gixhswlab1ppm/ppm/device/swing_full.png

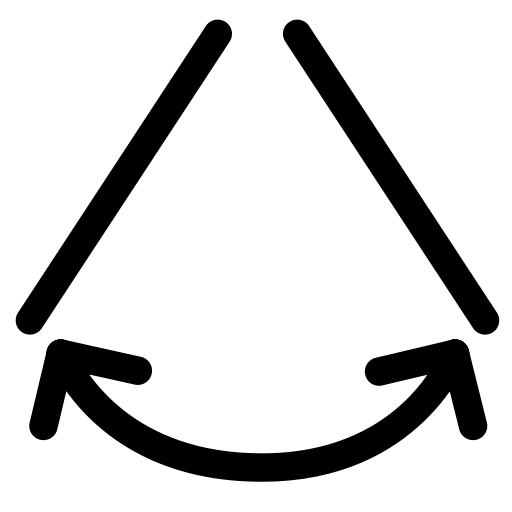
device/swing_full.png
