gixhswlab1ppm/ppm/device/thumb.png

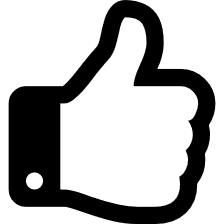
device/thumb.png
