gixhswlab1ppm/ppm/device/wave_full.png

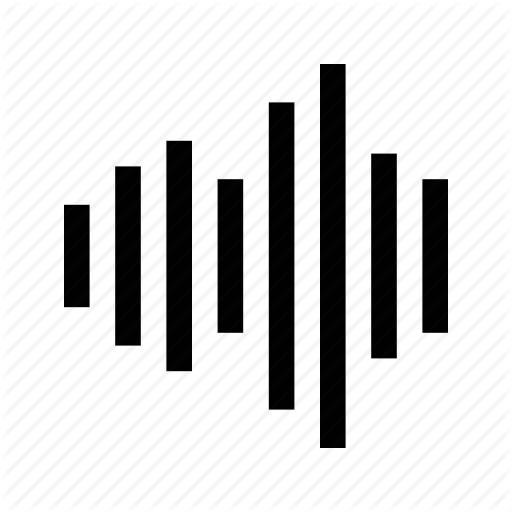
device/wave_full.png
