gixhswlab1ppm/ppm/insights/Figure_1.png

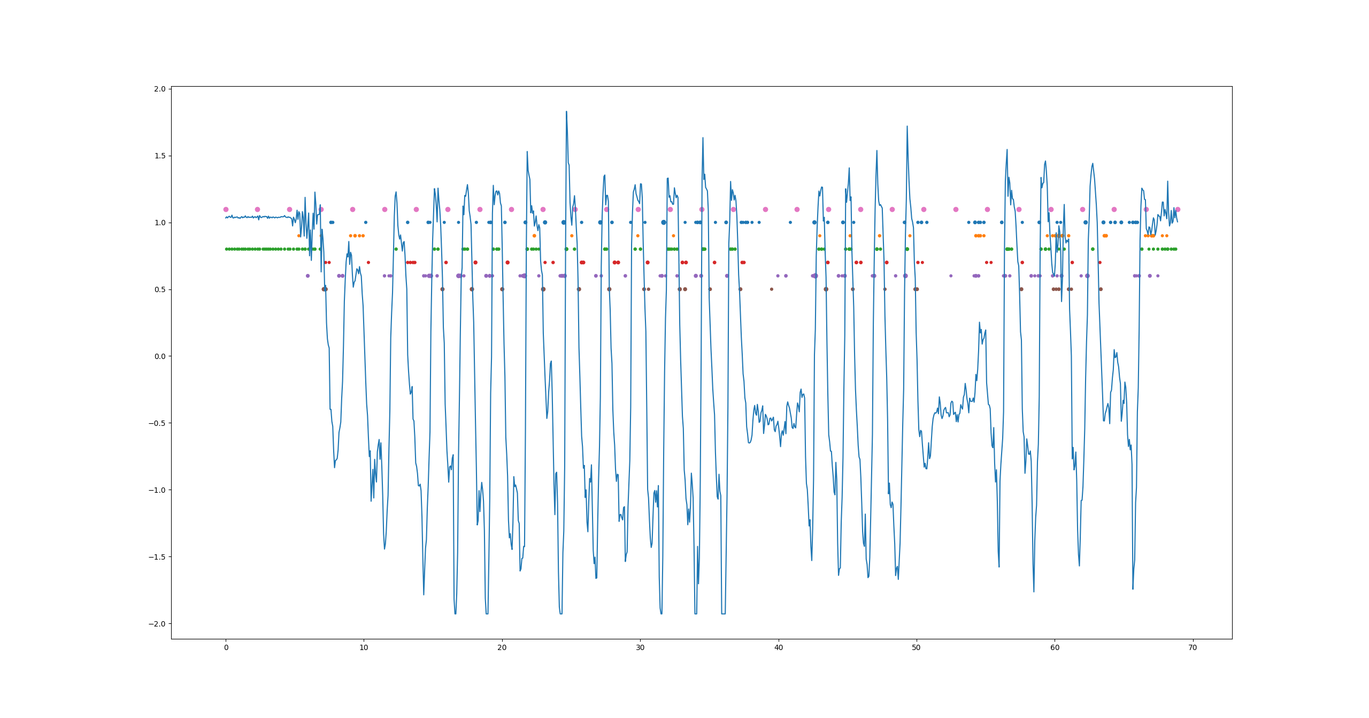
insights/Figure_1.png
