gixhswlab1ppm/ppm/insights/Figure_4.png

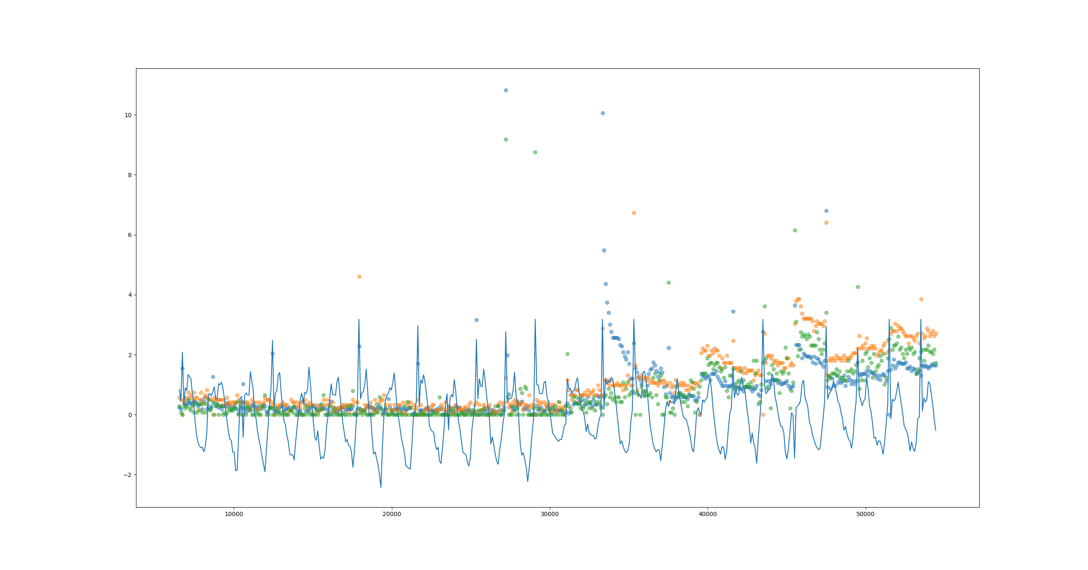
insights/Figure_4.png
