gixhswlab1ppm/ppm/insights/Figure_5.png

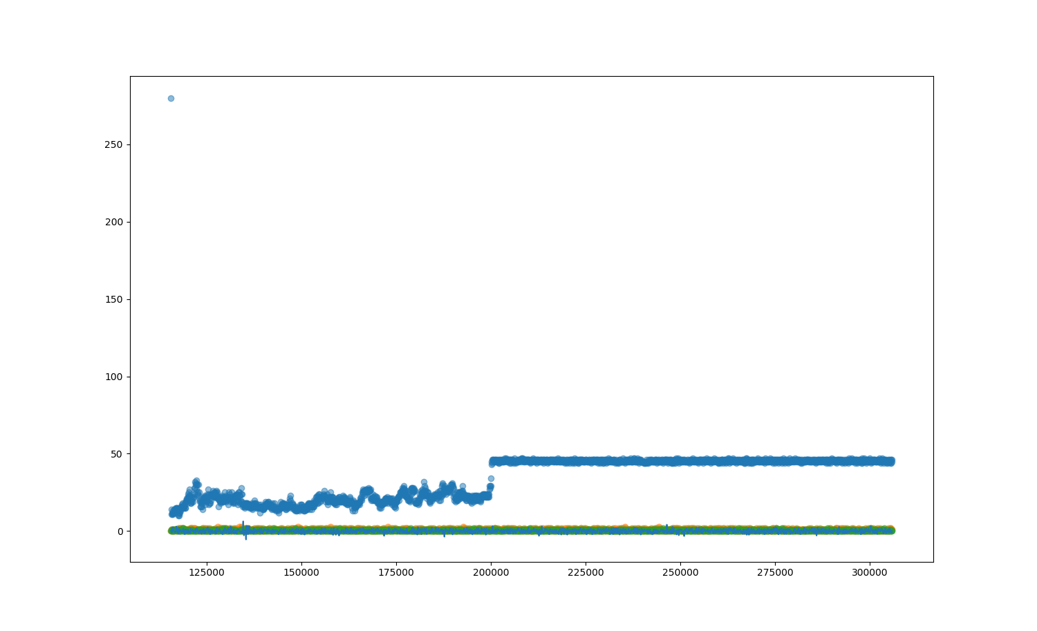
insights/Figure_5.png
