gixhswlab1ppm/ppm/insights/Figure_6.png

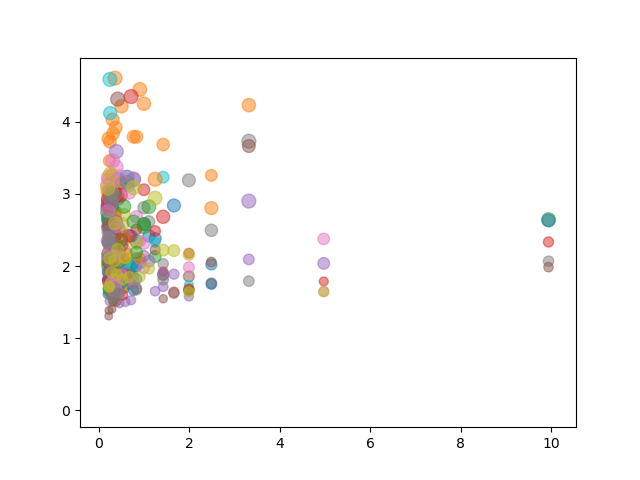
insights/Figure_6.png
