gixhswlab1ppm/ppm/insights/Figure_7.png

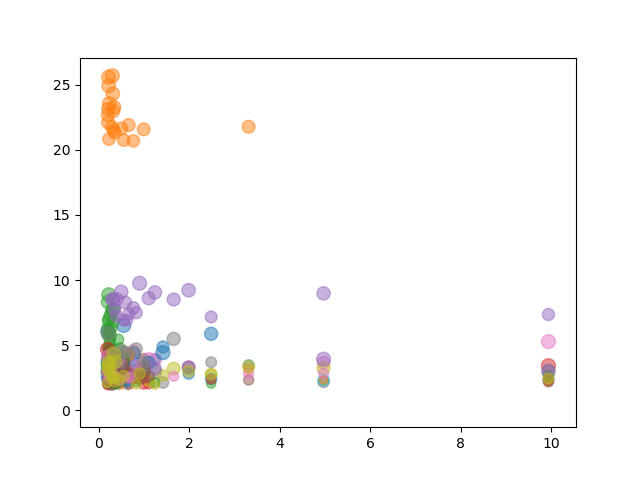
insights/Figure_7.png
