gixhswlab1ppm/ppm/insights/Figure_9.png

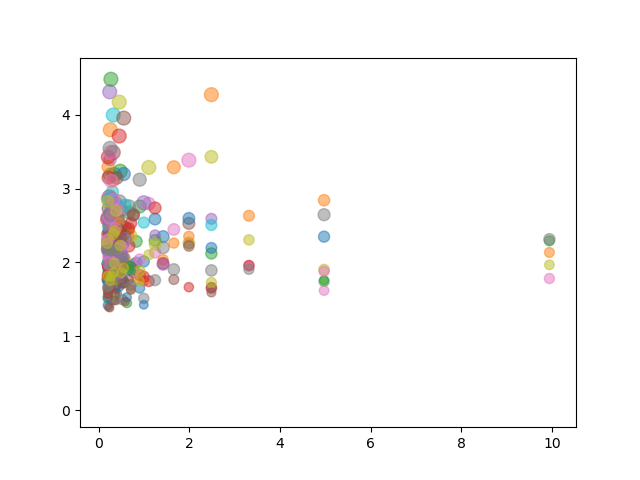
insights/Figure_9.png
