gixhswlab1ppm/ppm/insights/Figure_11.png

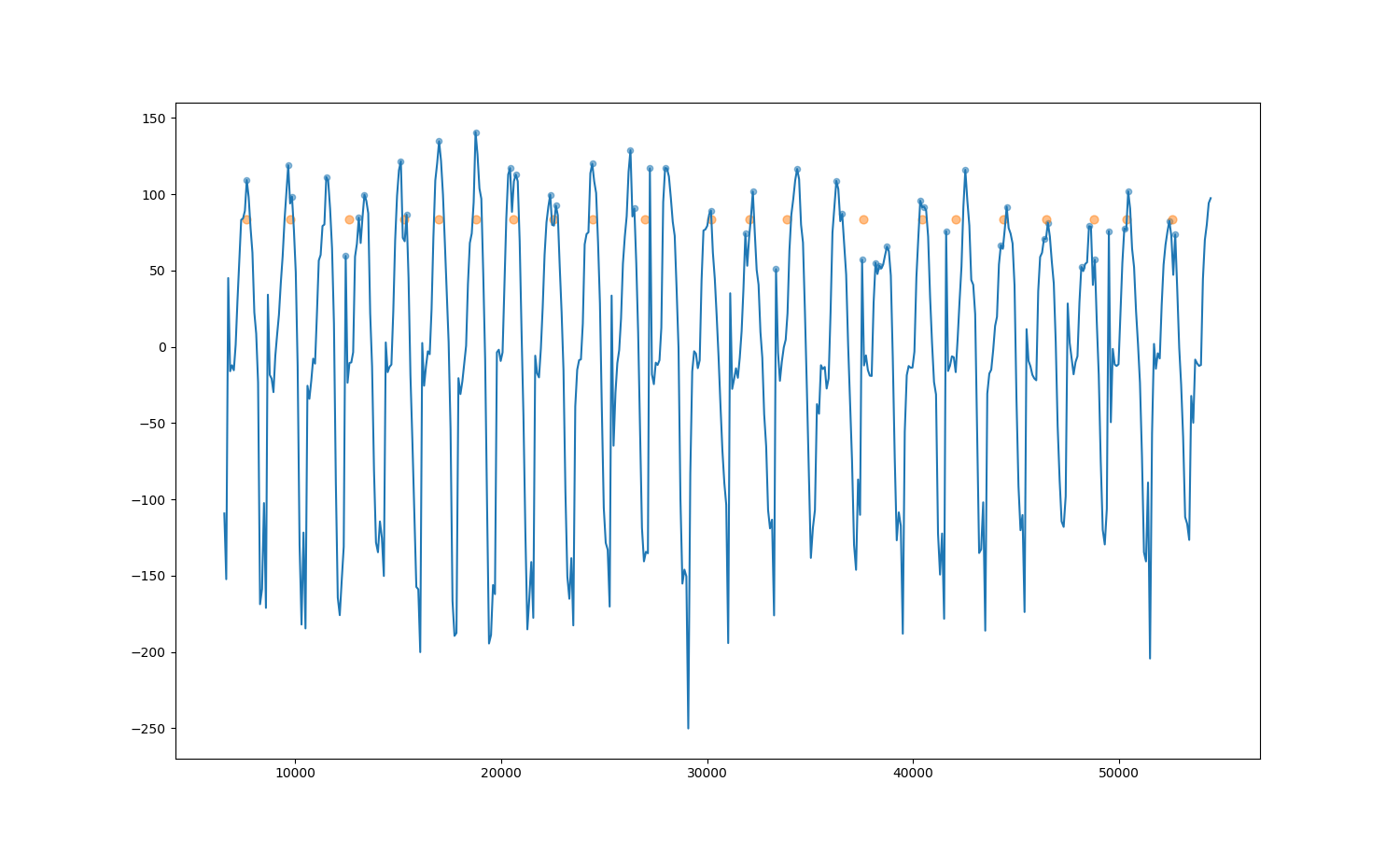
insights/Figure_11.png
