gixhswlab1ppm/ppm/insights/Figure_12.png

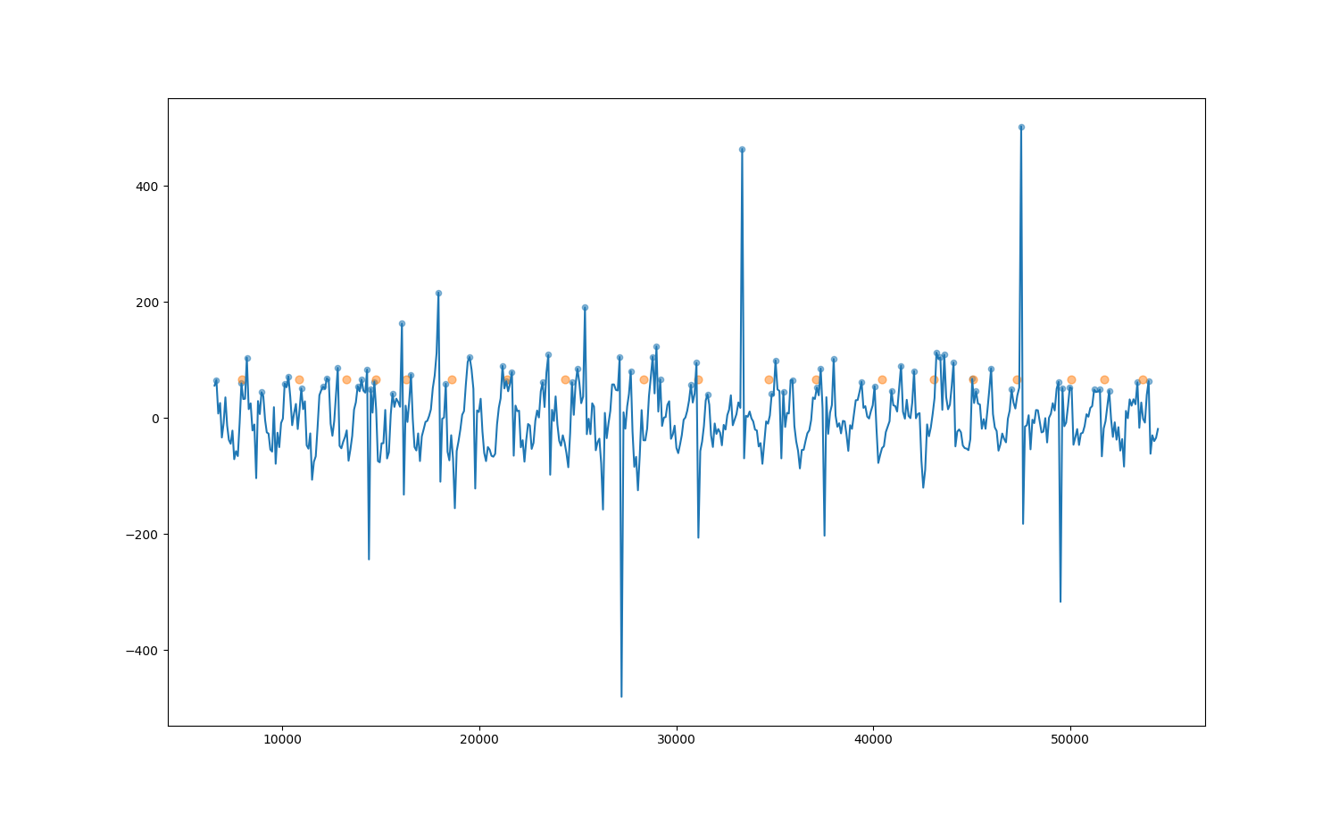
insights/Figure_12.png
