gixhswlab1ppm/ppm/insights/Figure_13.png

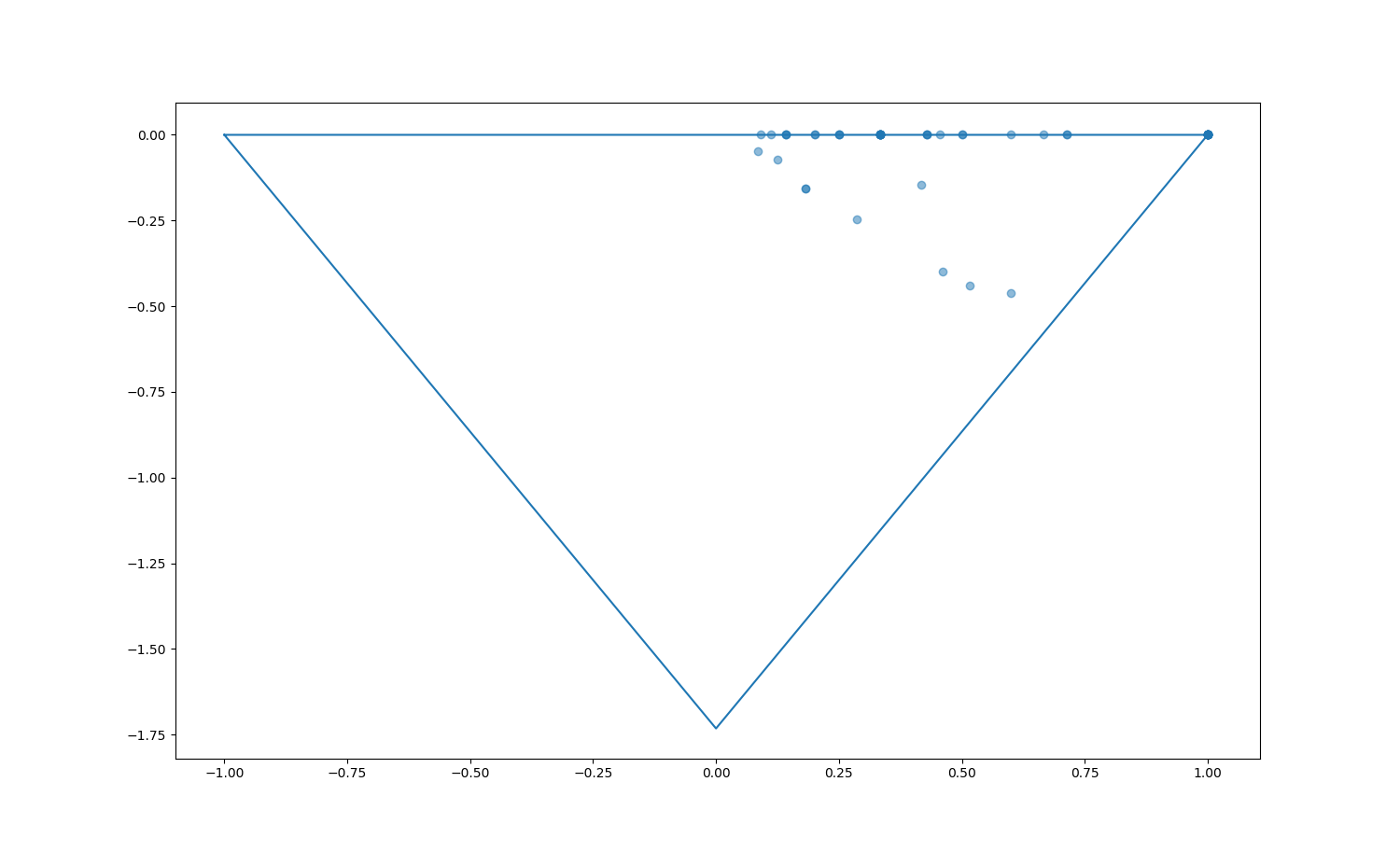
insights/Figure_13.png
