gixhswlab1ppm/ppm/insights/Figure_14.png

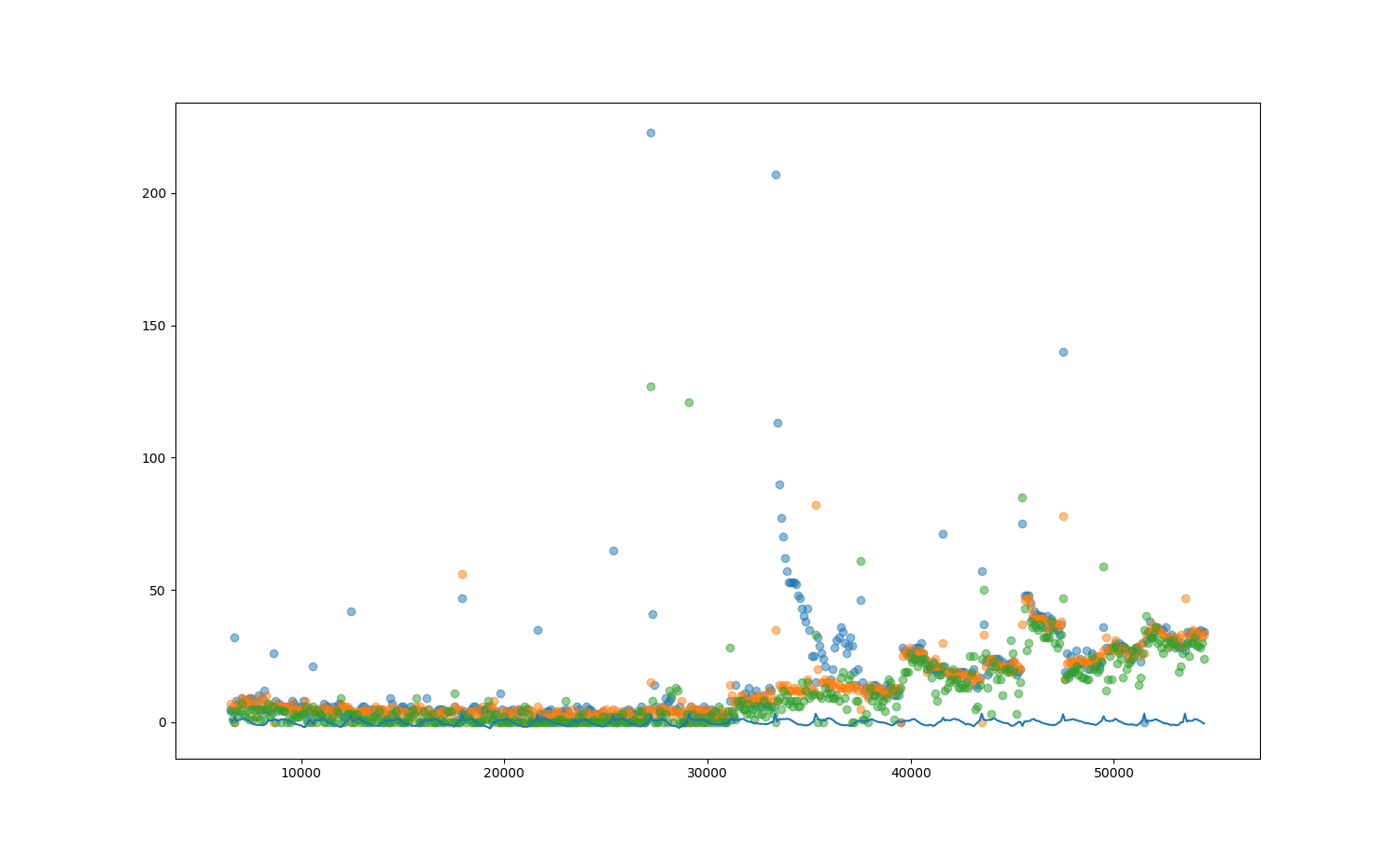
insights/Figure_14.png
