gixhswlab1ppm/ppm/insights/Figure_15.png

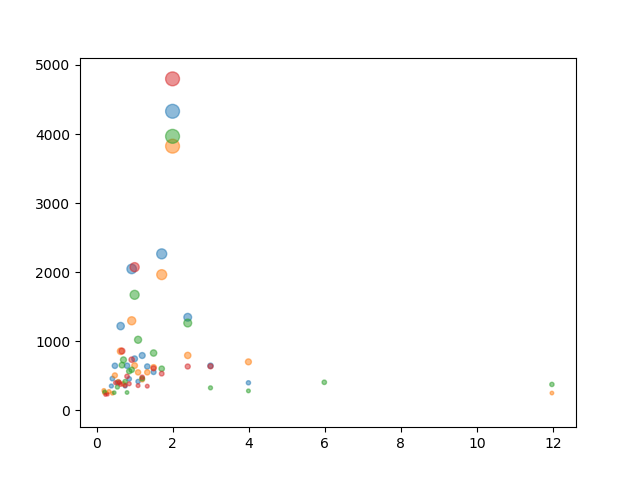
insights/Figure_15.png
