gixhswlab1ppm/ppm/insights/Figure_16.png

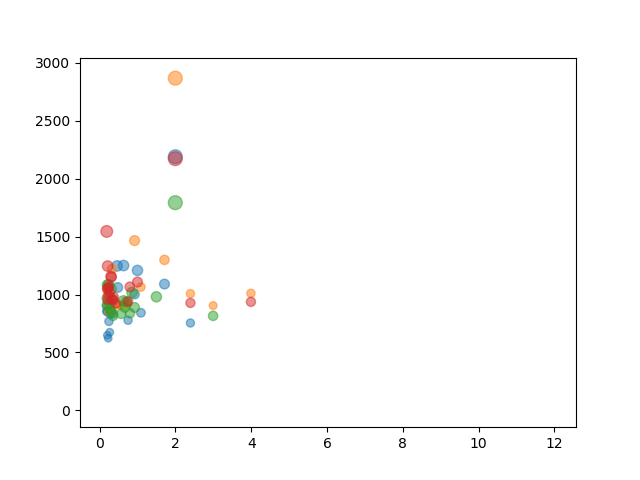
insights/Figure_16.png
