gixhswlab1ppm/ppm/insights/Figure_17.png

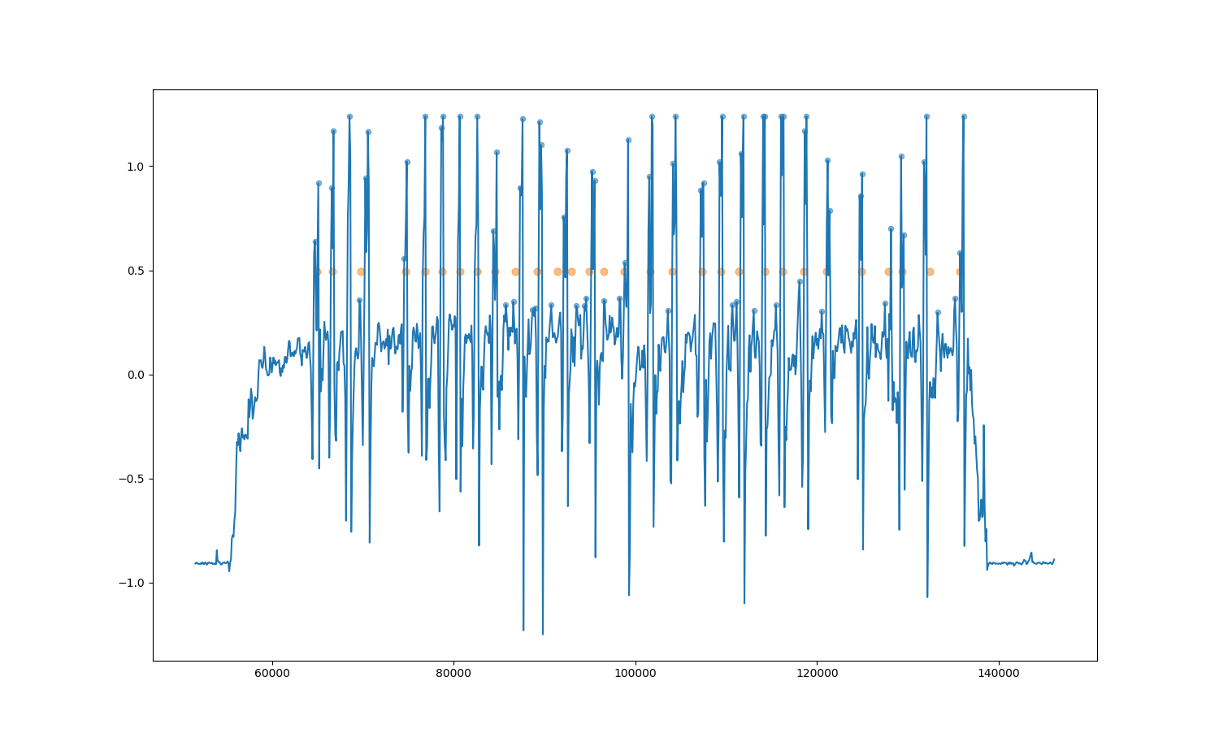
insights/Figure_17.png
