gixhswlab1ppm/ppm/insights/Figure_18.png

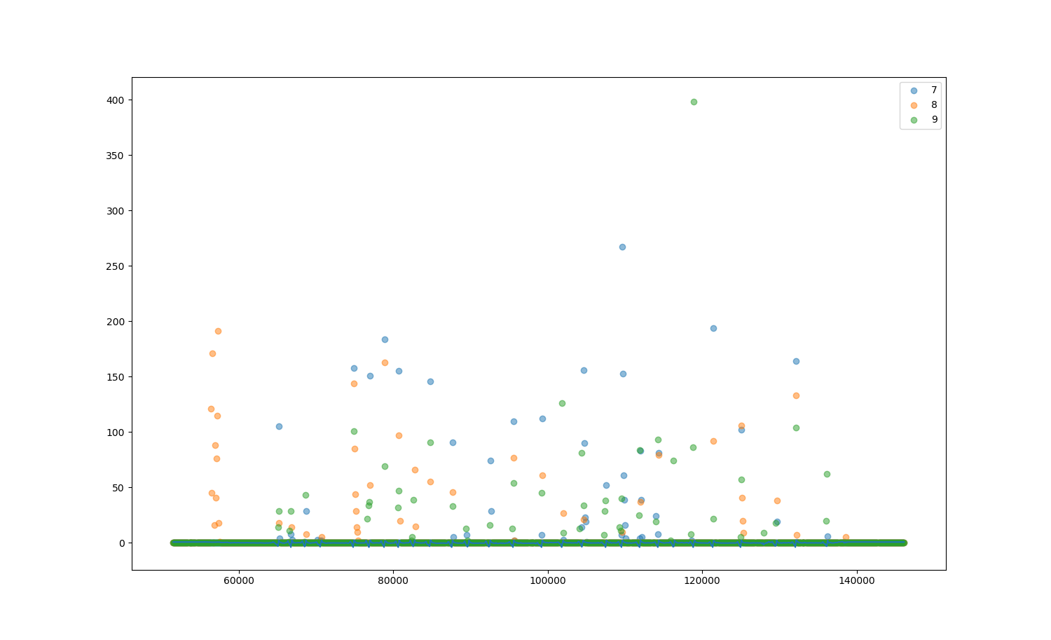
insights/Figure_18.png
