gixhswlab1ppm/ppm/insights/Figure_19.png

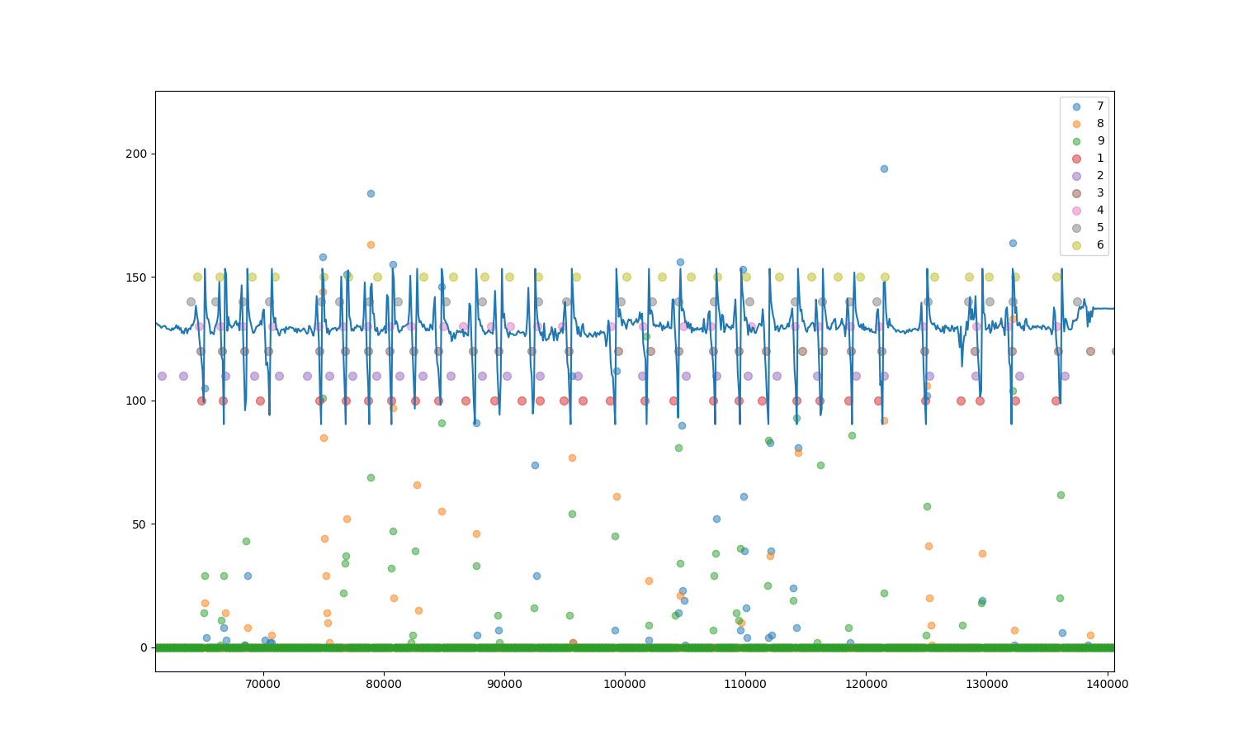
insights/Figure_19.png
