gixhswlab1ppm/ppm/insights/Figure_21.png

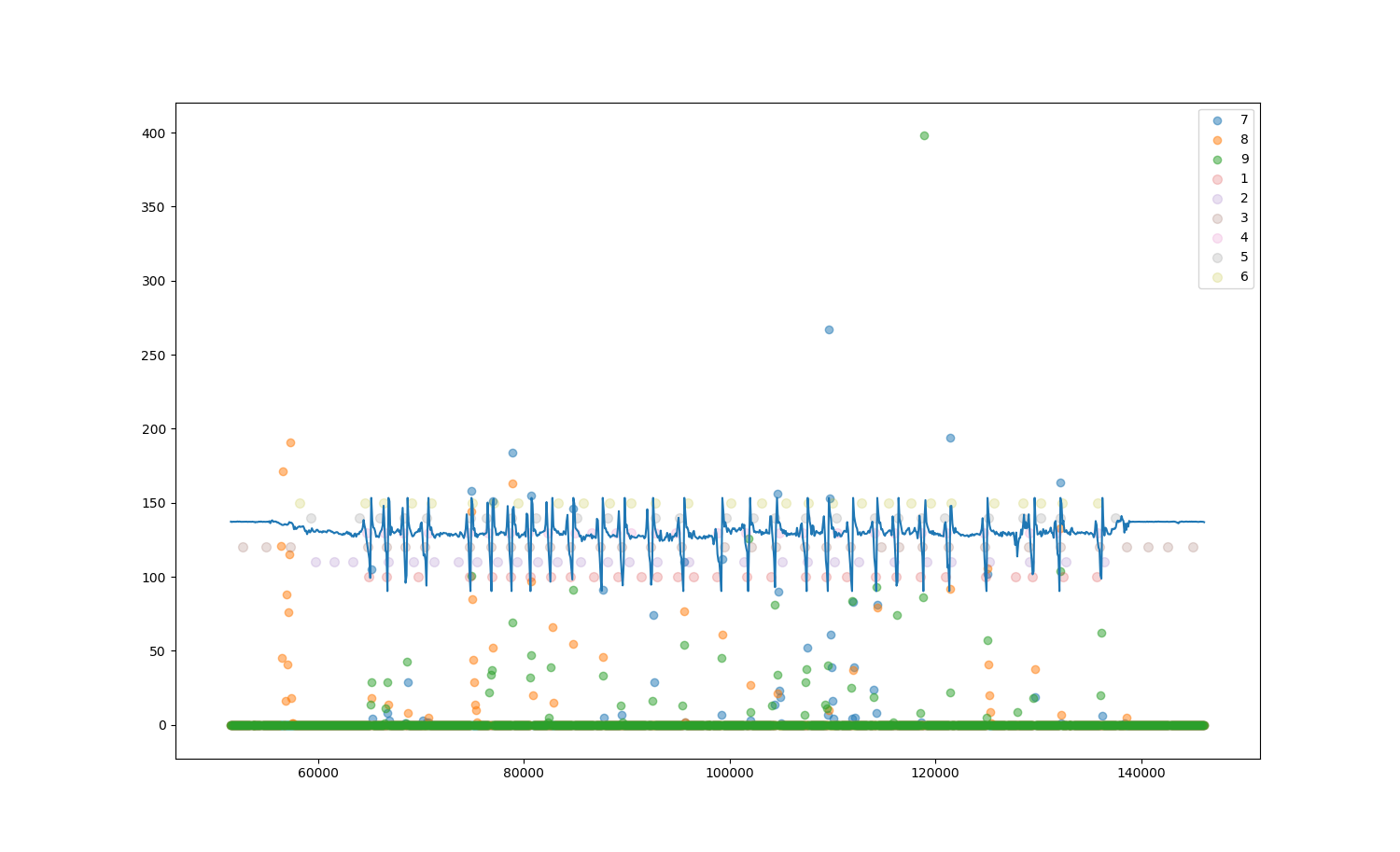
insights/Figure_21.png
