gixhswlab1ppm/ppm/insights/Figure_22.png

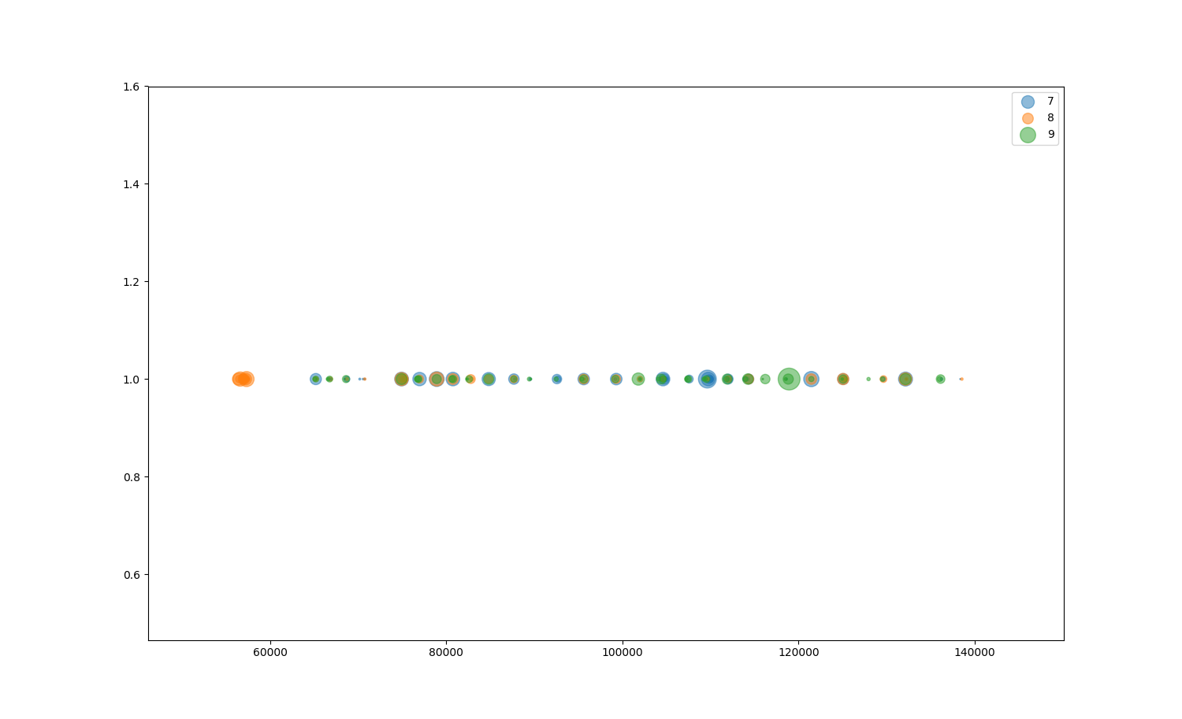
insights/Figure_22.png
