gixhswlab1ppm/ppm/insights/Figure_24.png

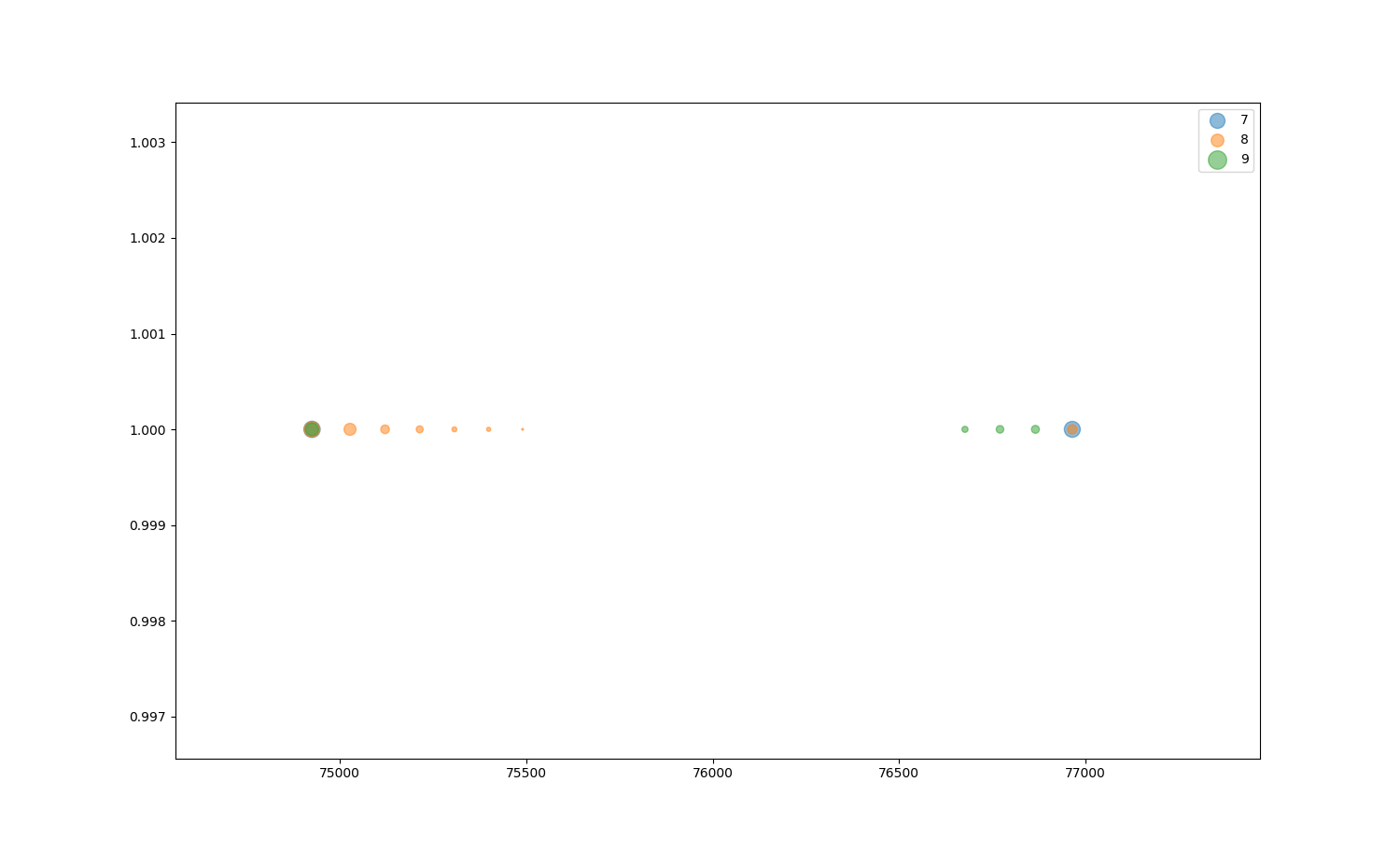
insights/Figure_24.png
