gixhswlab1ppm/ppm/insights/Figure_26.png

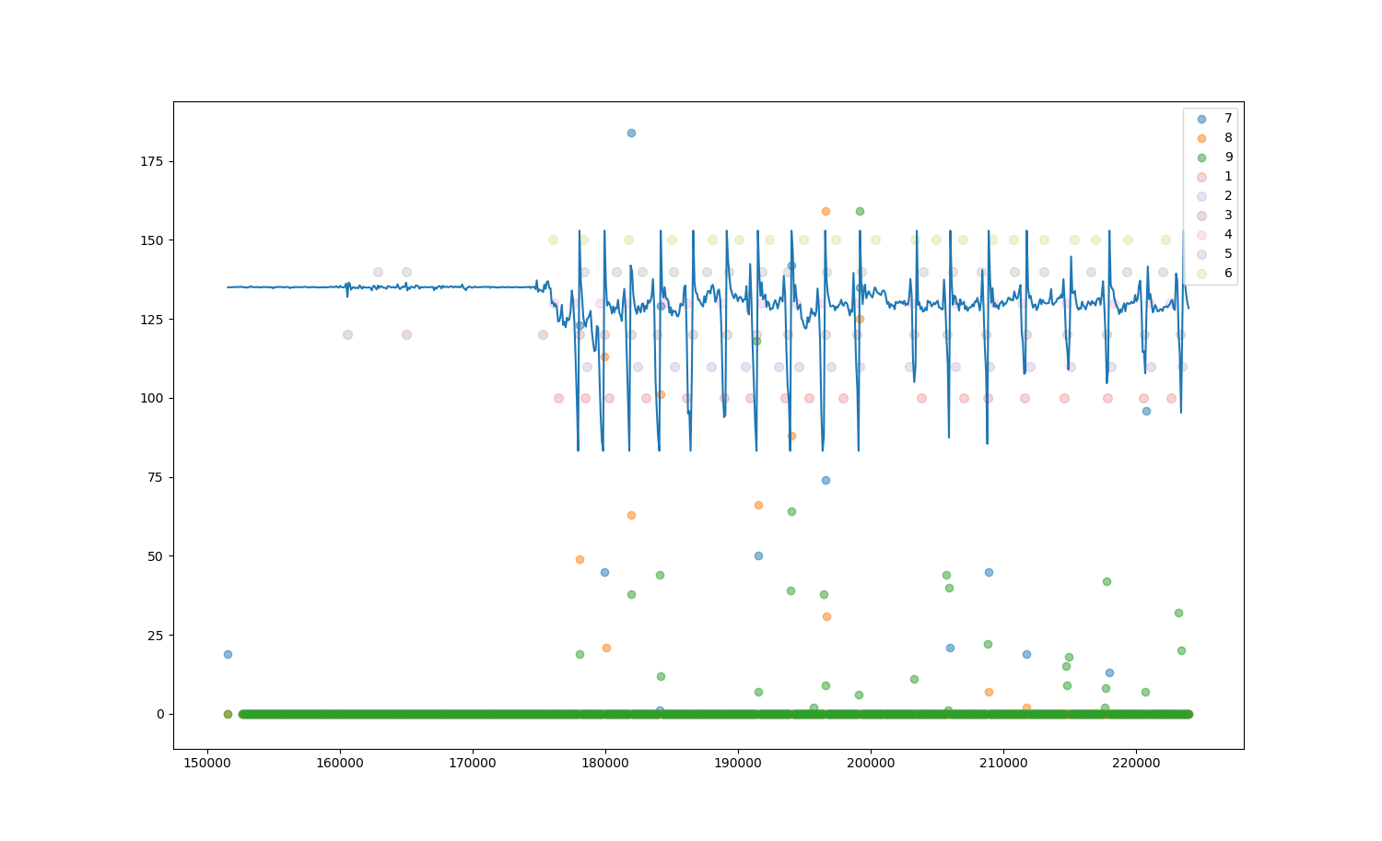
insights/Figure_26.png
