gixhswlab1ppm/ppm/insights/Figure_27.png

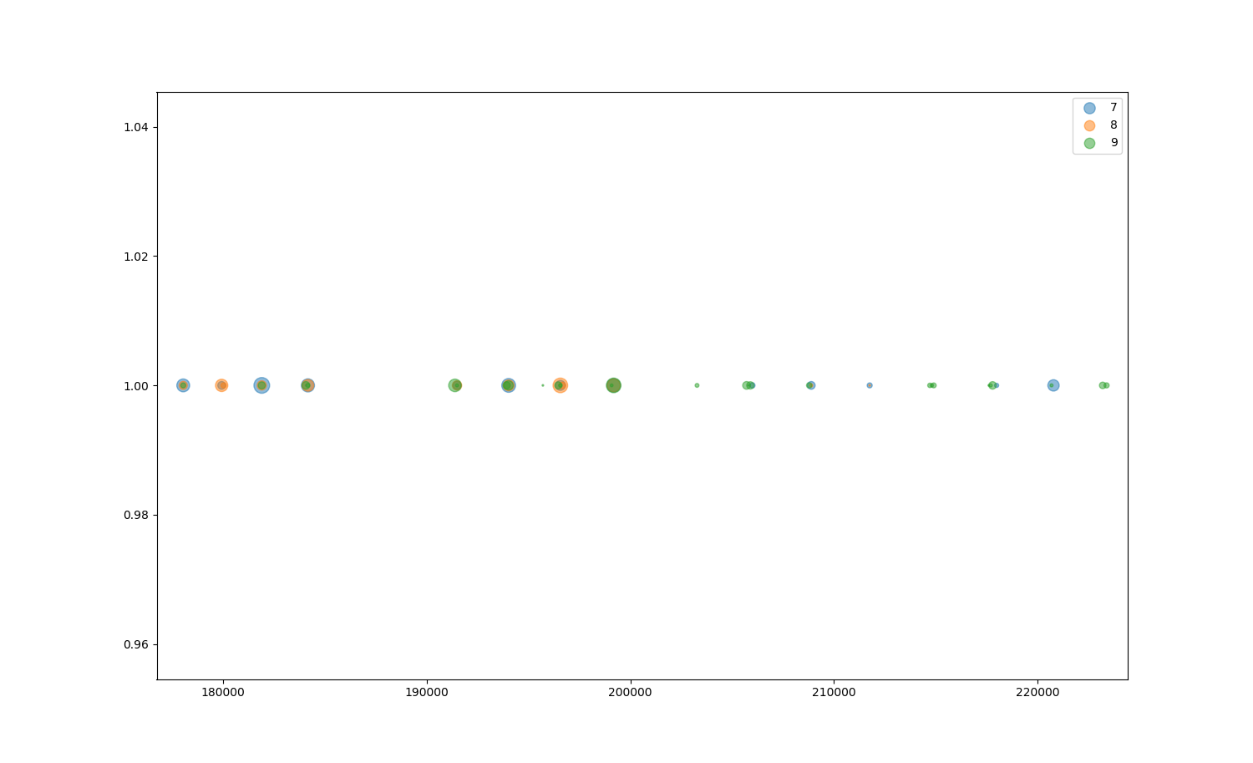
insights/Figure_27.png
