gixhswlab1ppm/ppm/insights/Figure_29.png

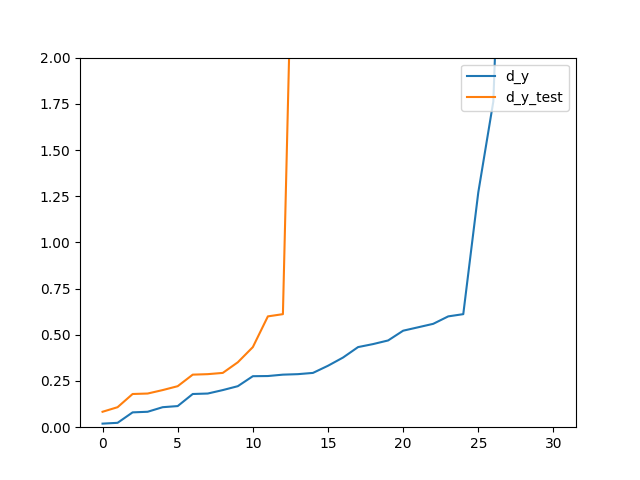
insights/Figure_29.png
