gixhswlab1ppm/ppm/insights/Figure_31.png

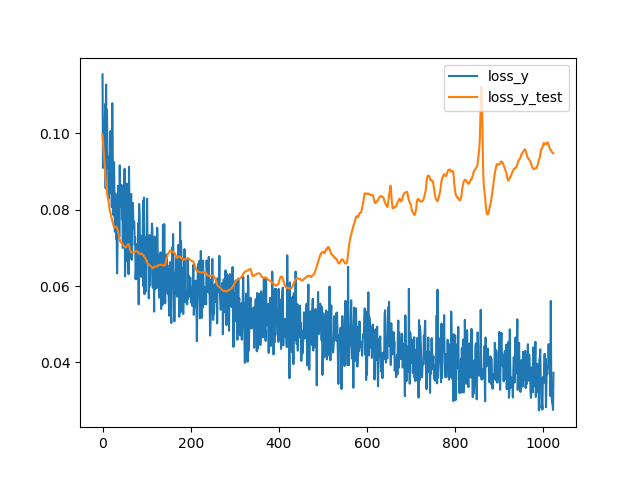
insights/Figure_31.png
