gixhswlab1ppm/ppm/insights/Figure_32.png

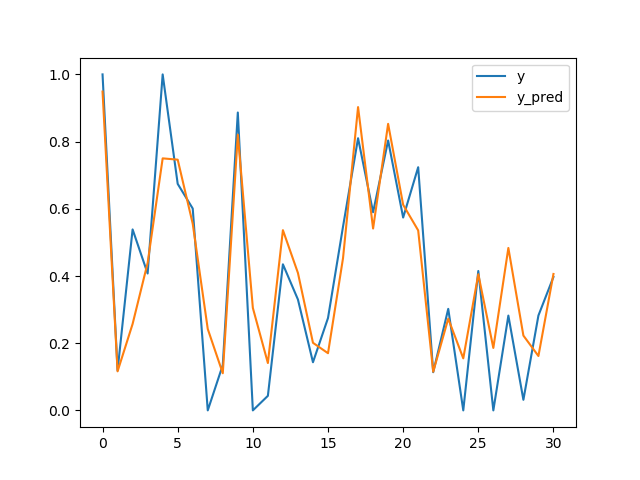
insights/Figure_32.png
