gixhswlab1ppm/ppm/insights/Figure_33.png

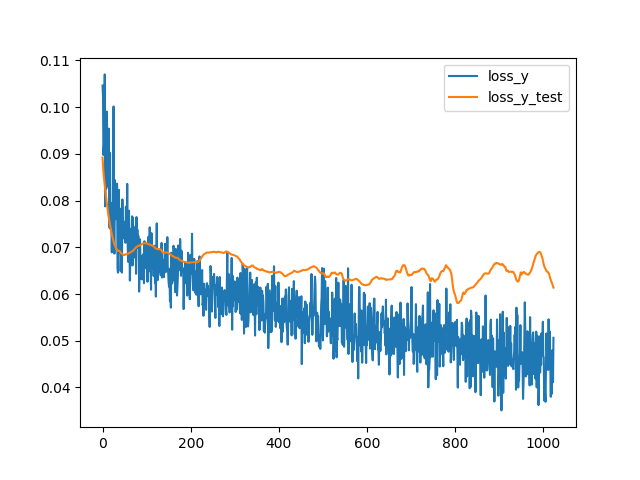
insights/Figure_33.png
