gixhswlab1ppm/ppm/insights/Figure_35.png

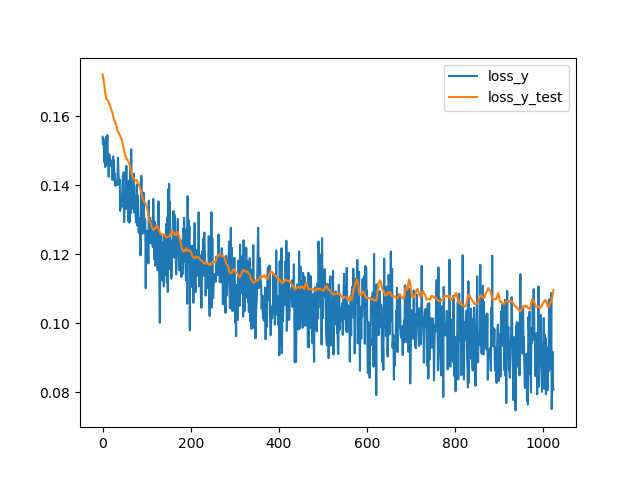
insights/Figure_35.png
