gixhswlab1ppm/ppm/insights/Figure_36.png

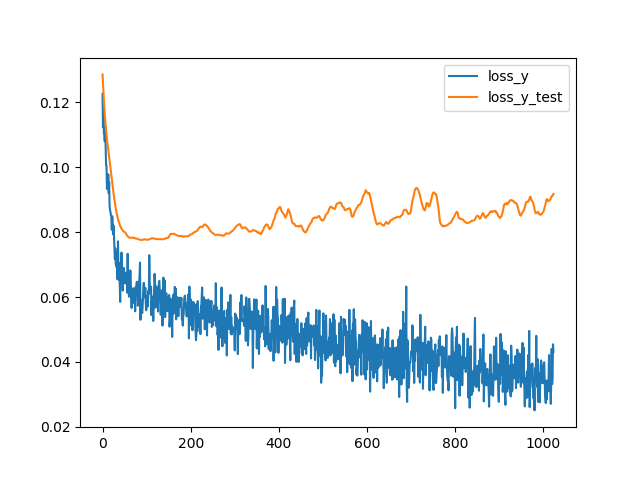
insights/Figure_36.png
