gixhswlab1ppm/ppm/insights/Figure_38.png

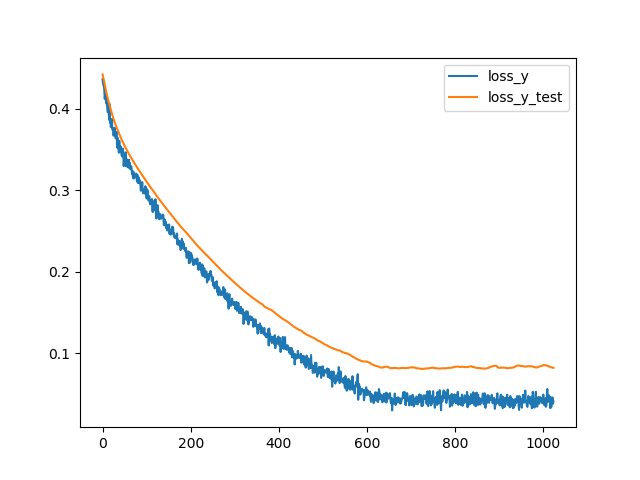
insights/Figure_38.png
