gixhswlab1ppm/ppm/insights/Figure_39.png

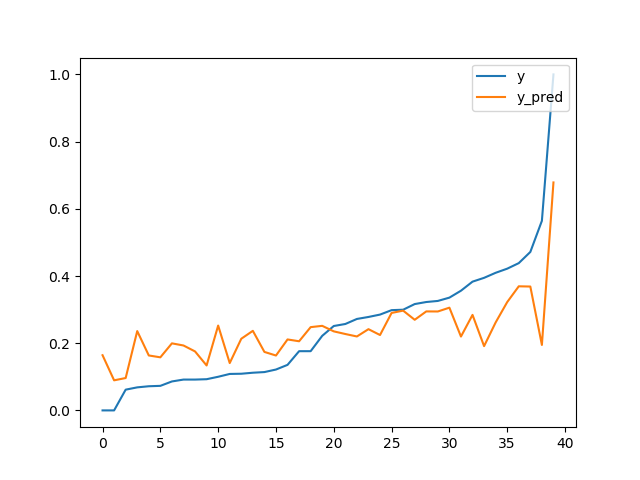
insights/Figure_39.png
