gixhswlab1ppm/ppm/insights/Figure_41.png

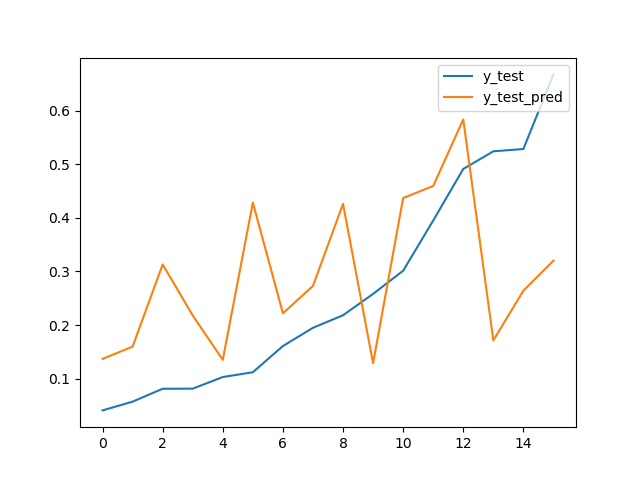
insights/Figure_41.png
