gixhswlab1ppm/ppm/insights/Figure_42.png

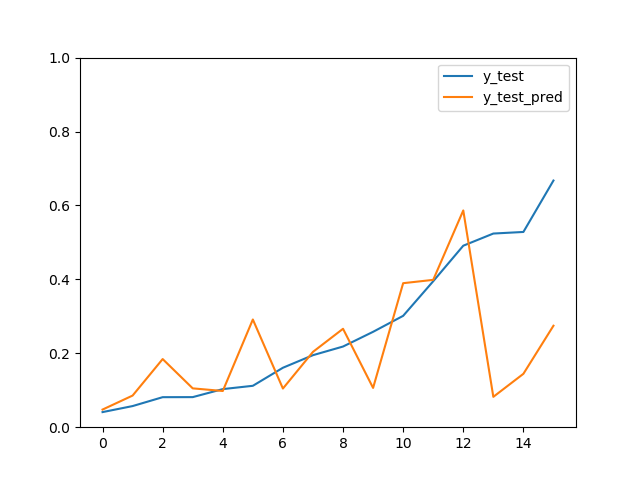
insights/Figure_42.png
