gixhswlab1ppm/ppm/insights/Screenshot from 2019-02-17 18-22-37.png

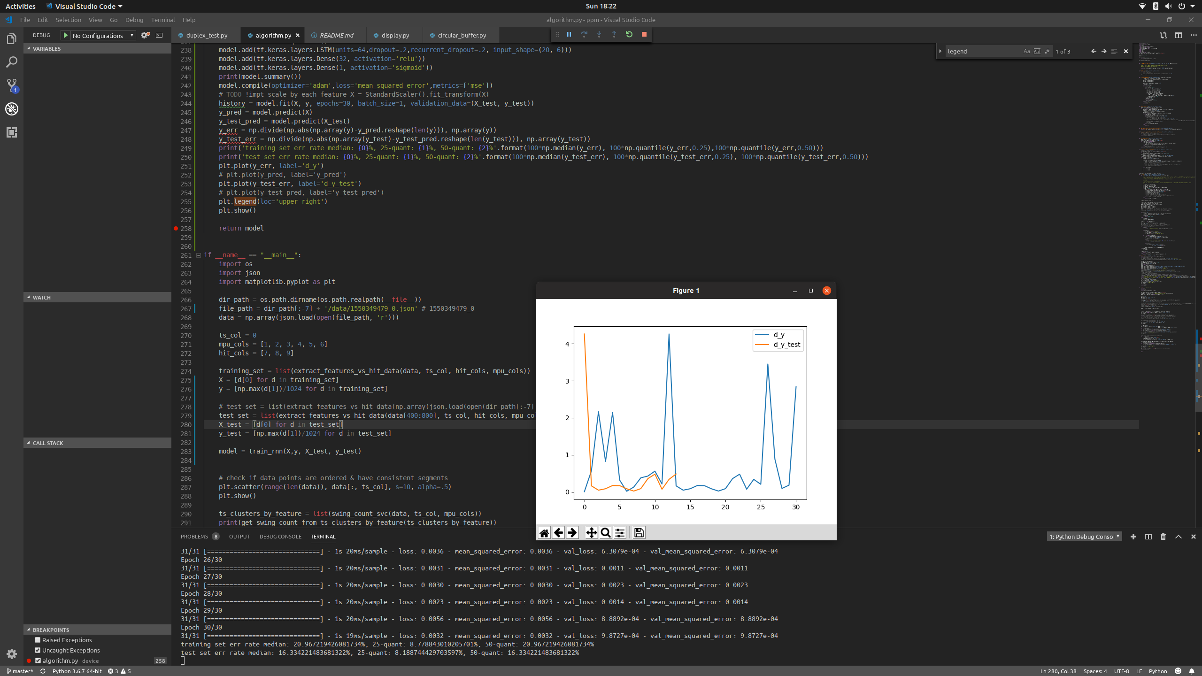
insights/Screenshot from 2019-02-17 18-22-37.png
