gixhswlab1ppm/ppm/device/profile_manager.py

import json
import os
class profile_manager:
    # fields = ["id", "th"]
    
    def __init__(self, file_path):
        self.profiles = json.load(open(file_path, 'r'))
        self.file_path = file_path
        self.profile_id = 4

    def _get_index(self, _id):
        return [i for i, p in enumerate(self.profiles) if p["id"] == _id][0]

    def update_id(self, _id):
        self.profile_id = _id

    def update(self, profile):
        self.profiles[self._get_index(self.profile_id)] = profile
        import ujson
        ujson.dump(self.profiles, open(self.file_path, 'w'))

    def update_field(self, field, val):
        profile = self.profiles[self._get_index(self.profile_id)]
        profile[field] = val
        self.update(profile)

    def get_field(self, field):
        if field in self.profiles[self._get_index(self.profile_id)]:
            return self.profiles[self._get_index(self.profile_id)][field]
        else:
            return None

    def get_id(self):
        return self.profile_id

    def get_len(self):
        return 5
